OPEnSLab-OSU/OPEnS-Hypnos/EAGLE CAD/OPEnS-Power-1.0.0.brd

## EAGLE design EAGLE CAD/OPEnS-Power-1.0.0.brd (2019-01-03)

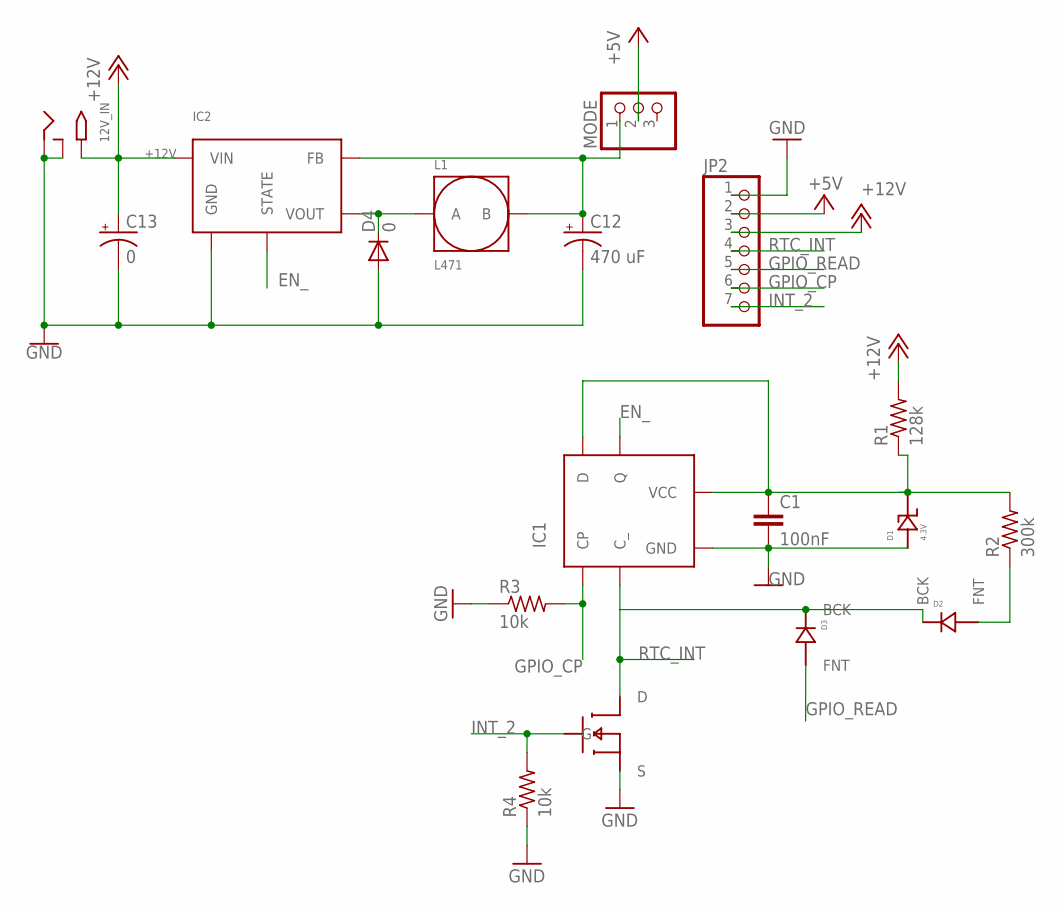
[picture p35: schematic OPEnS-Power-1.0.0.sch]

Parts:
12V_IN: 2.1MMJACKSMT; DCJACK_2MM_SMT
C1: 100nF; C0805
C12: 470 uF; 153CLV-0810
C13: 0; 153CLV-0505
D1: 4.3V; DO-219AC
D2, D3: DIODE-DO-214AC
D4: 0; DO41-10
IC1: NC7SZ175; SC70
IC2: LM2575; TO-263
JP2: PINHD-1X7; 1X07
L1: L471; 12-12
MODE: PINHD-1X3; 1X03
Q1: MOSFET-SOT23F; SOT-23F
R1: 128k; R0805
R2: 300k; R0805
R3, R4: 10k; R0805

Connections:
5_RAW: C12.+, IC2.FB, L1.B, MODE.1
+5V: JP2.2, MODE.2
+12V: 12V_IN.PWR2 (TIP), C13.+, IC2.VIN, JP2.3, R1.2
EN_: IC1.Q, IC2.STATE
GND: 12V_IN.GND (RING), 12V_IN.GNDBREAK (RING_SW), C1.2, C12.-, C13.-, D1.BCK, D4.A, IC1.GND, IC2.GND, JP2.1, Q1.S, R3.1, R4.1
GPIO_CP: IC1.CP, JP2.6, R3.2
GPIO_READ: D3.FNT, JP2.5
INT_2: JP2.7, Q1.G, R4.2
unnamed: D4.C, IC2.VOUT, L1.A
unnamed: C1.1, D1.FNT, IC1.D, IC1.VCC, R1.1, R2.2
unnamed: D2.FNT, R2.1
RTC_INT: D2.BCK, D3.BCK, IC1.C_, JP2.4, Q1.D

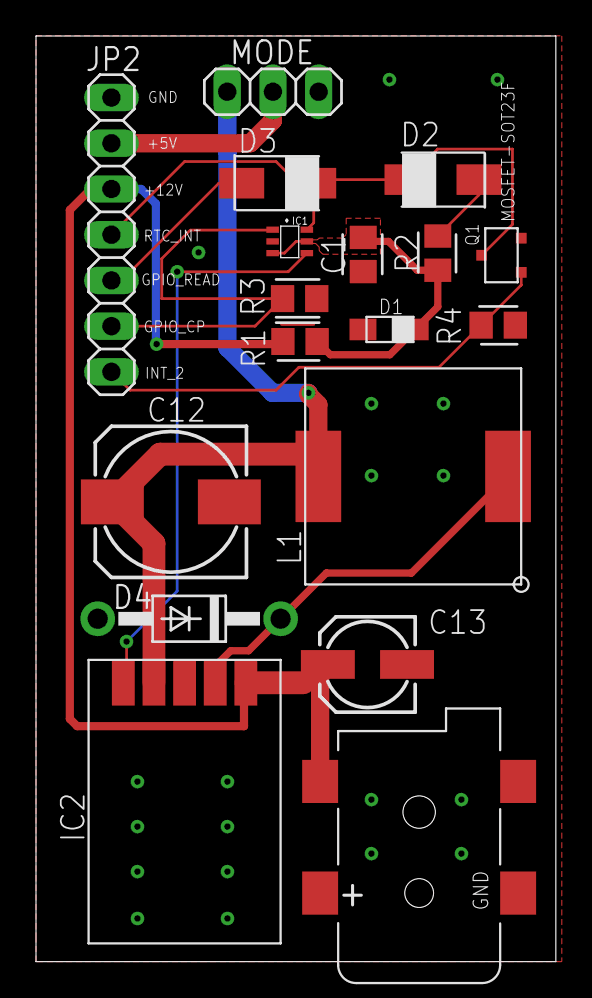
[picture p36: board OPEnS-Power-1.0.0.brd from above]

Board: 2 copper layers, 28.9 x 51.4 mm, 18 parts (0 on the bottom side), 12 nets.
